borisg912/3DNA/AppWindows/AssetsMigrate/contrast-black/LargeTile.scale-100.png

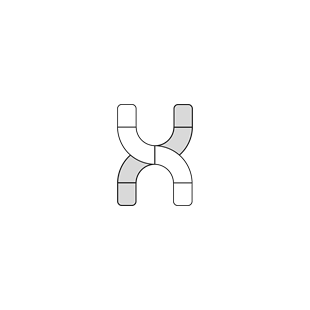
AppWindows/AssetsMigrate/contrast-black/LargeTile.scale-100.png
