borisg912/3DNA/AppWindows/AssetsMigrate/contrast-black/SmallTile.scale-200.png

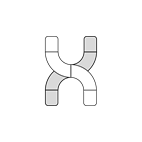
AppWindows/AssetsMigrate/contrast-black/SmallTile.scale-200.png
